18Markus1984/ESP_Logger/docs/images/hero_A.png

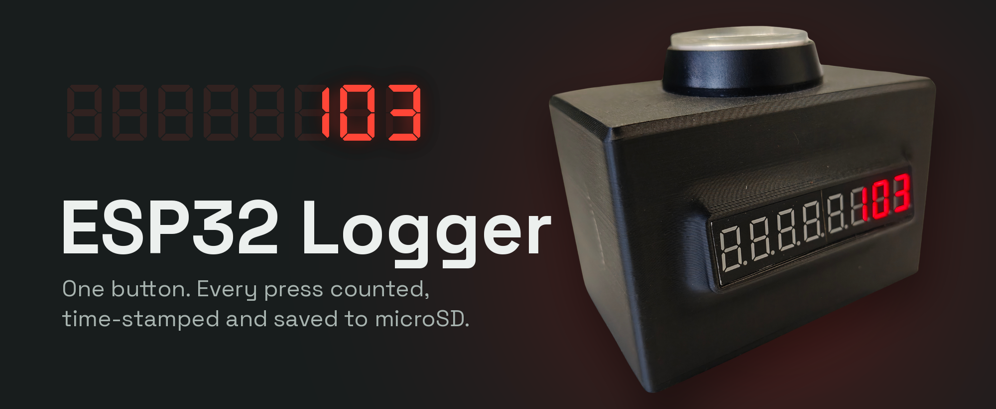
docs/images/hero_A.png
