18Markus1984/ESP_Logger/PCB/BesucherTasterPlatine/V1.3OhneCopperFill/BesucherZähler_etch_copper_top.pdf

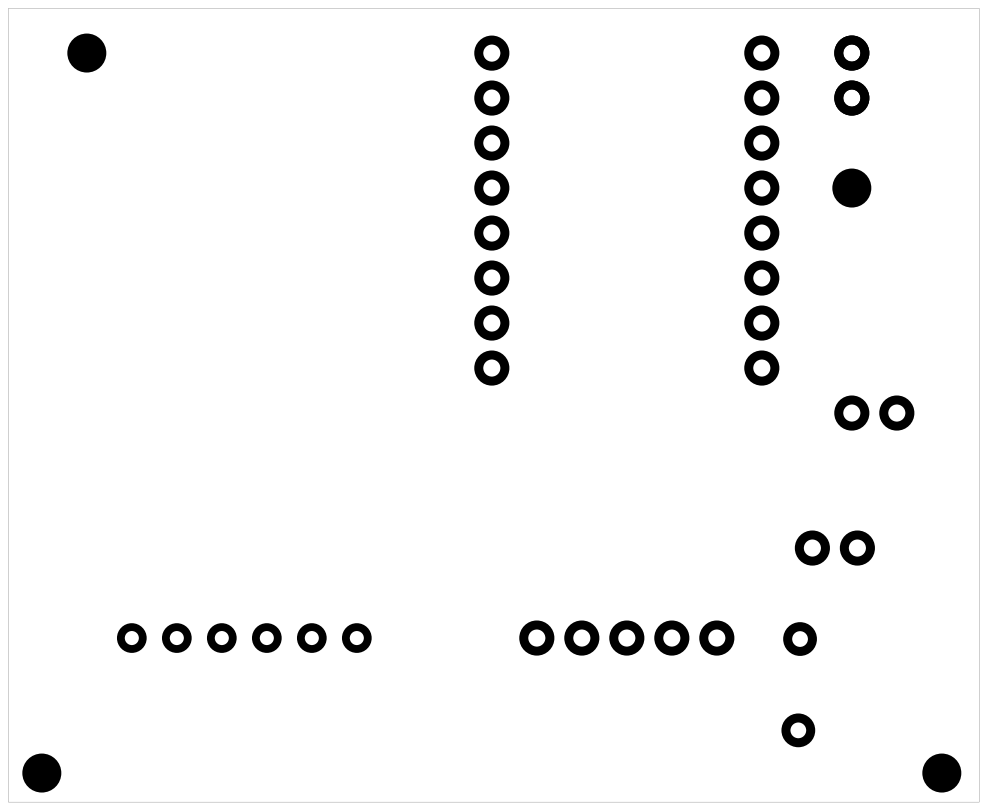
[picture p43: page 1]
