18Markus1984/ESP_Logger/PCB/BesucherTasterPlatine/V1.3OhneCopperFill/BesucherZähler_etch_copper_top_mirror.pdf

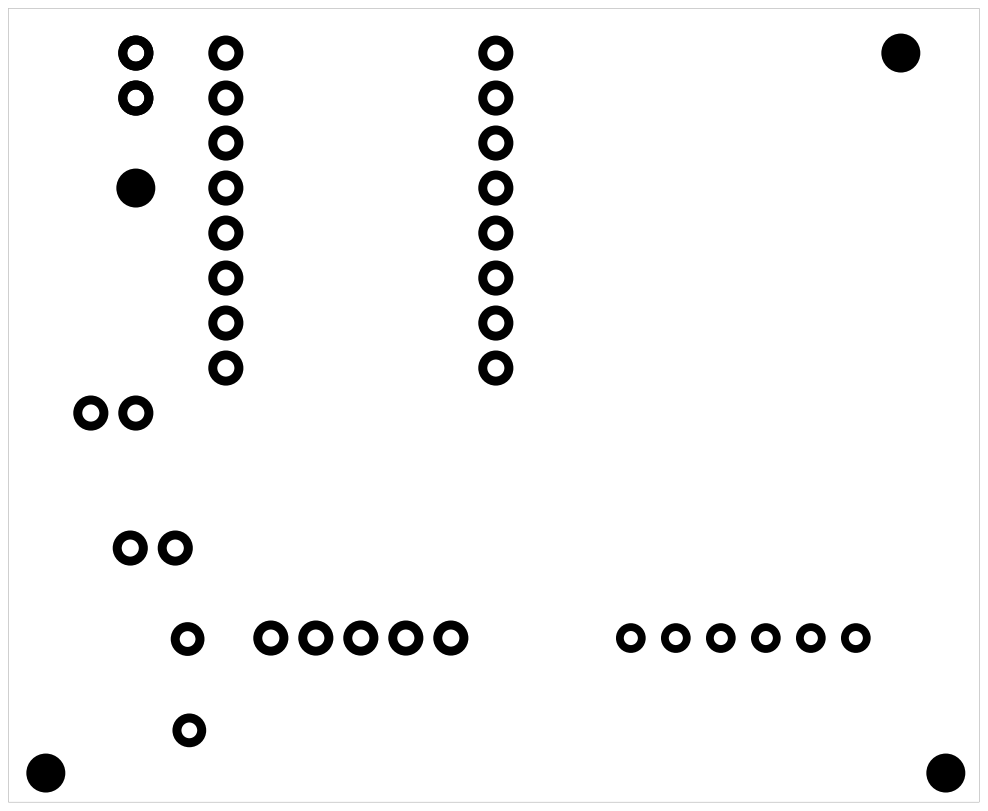
[picture p44: page 1]
