18Markus1984/ESP_Logger/PCB/BesucherTasterPlatine/V1.3OhneCopperFill/BesucherZähler_etch_mask_bottom.pdf

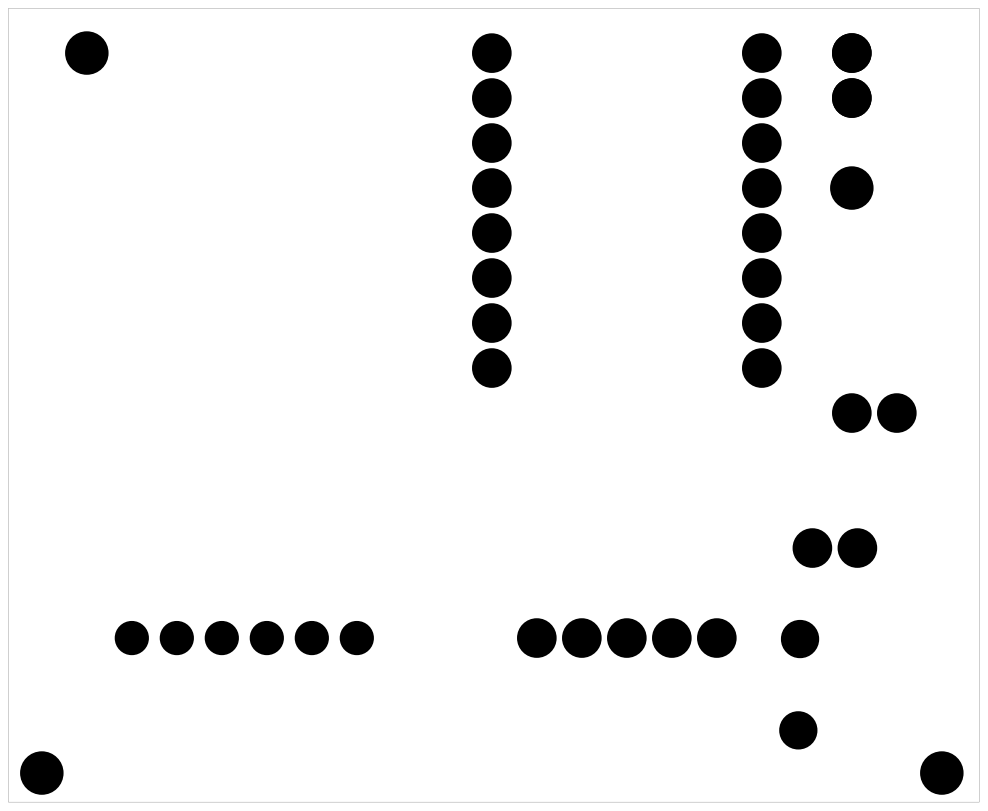
[picture p45: page 1]
