18Markus1984/ESP_Logger/PCB/BesucherTasterPlatine/V1.3OhneCopperFill/BesucherZähler_etch_mask_bottom_mirror.pdf

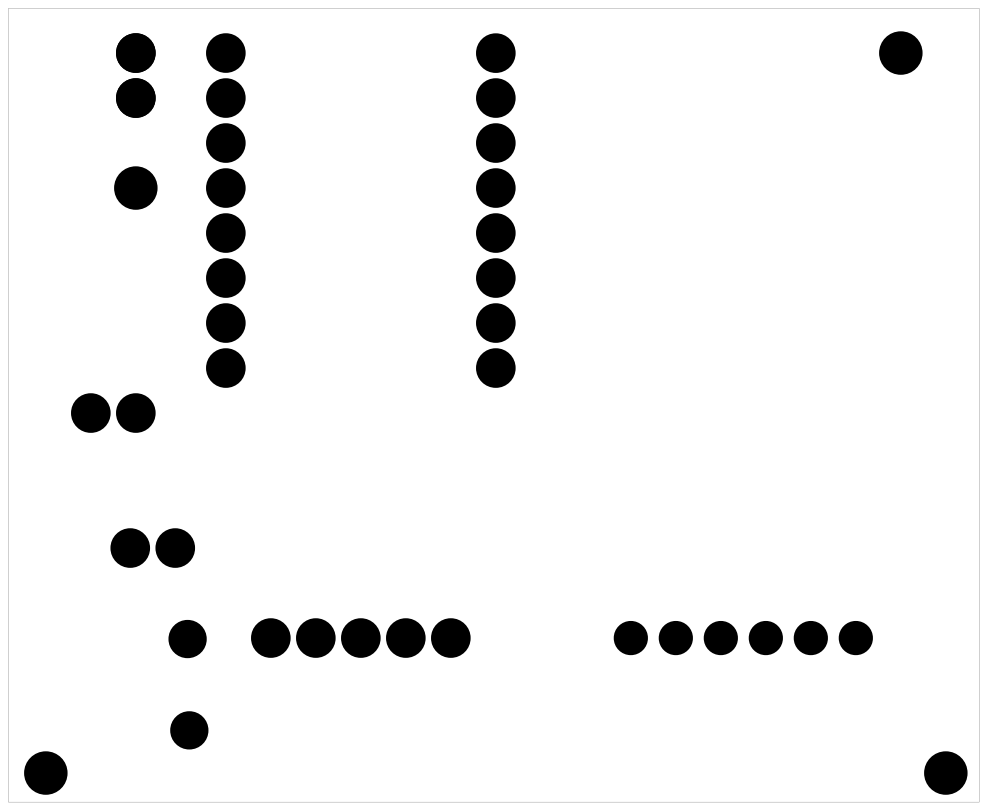
[picture p46: page 1]
