18Markus1984/ESP_Logger/PCB/BesucherTasterPlatine/V1.3OhneCopperFill/BesucherZähler_etch_silk_bottom.pdf

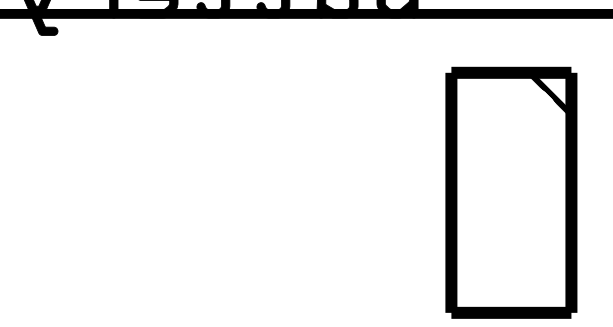
[picture p47: page 1]
