18Markus1984/ESP_Logger/PCB/BesucherTasterPlatine/V1.3OhneCopperFill/BesucherZähler_etch_silk_bottom_mirror.pdf

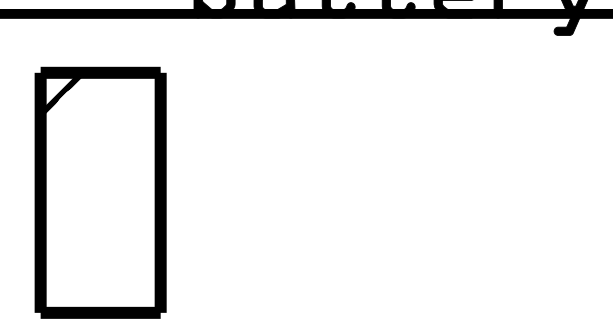
[picture p48: page 1]
