18Markus1984/ESP_Logger/PCB/BesucherTasterPlatine/V1.3OhneCopperFill/BesucherZähler_etch_silk_top_mirror.pdf

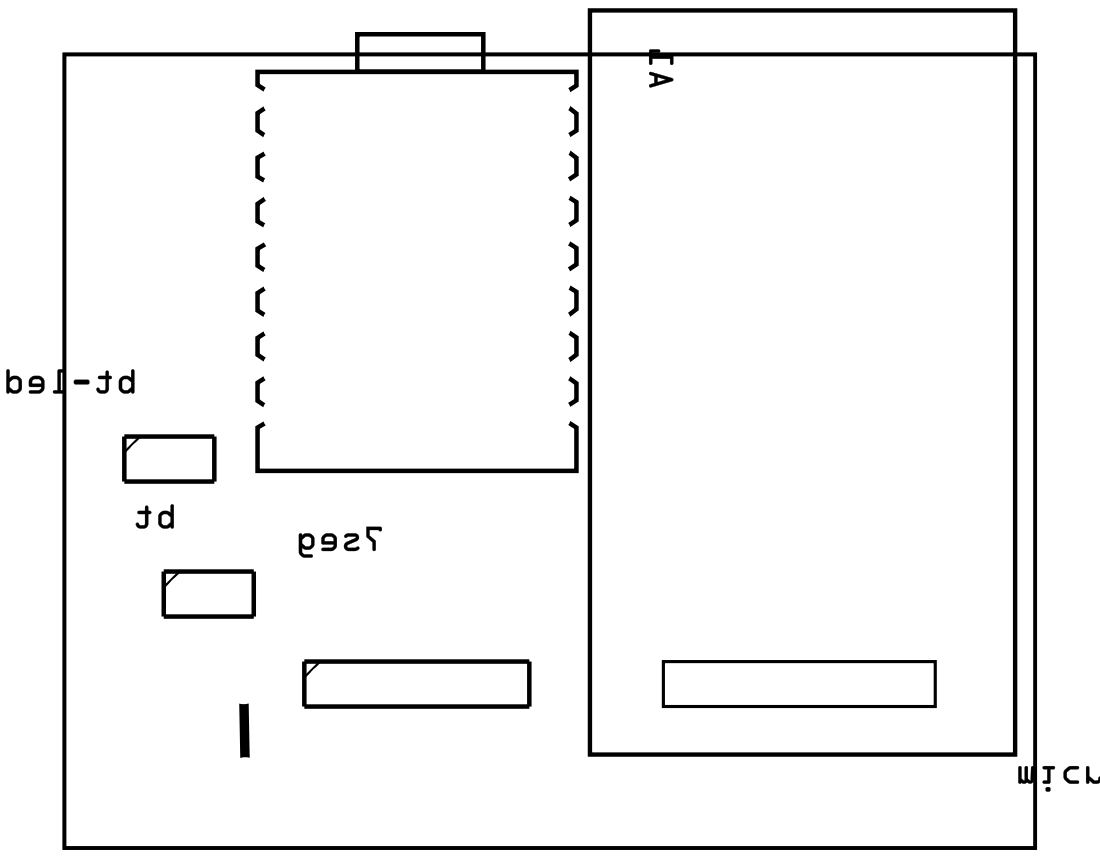
[picture p50: page 1]
