18Markus1984/ESP_Logger/PCB/BesucherTasterPlatine/V2.2_S2Mini/BesucherZählerS2Mini_etch_copper_bottom.pdf

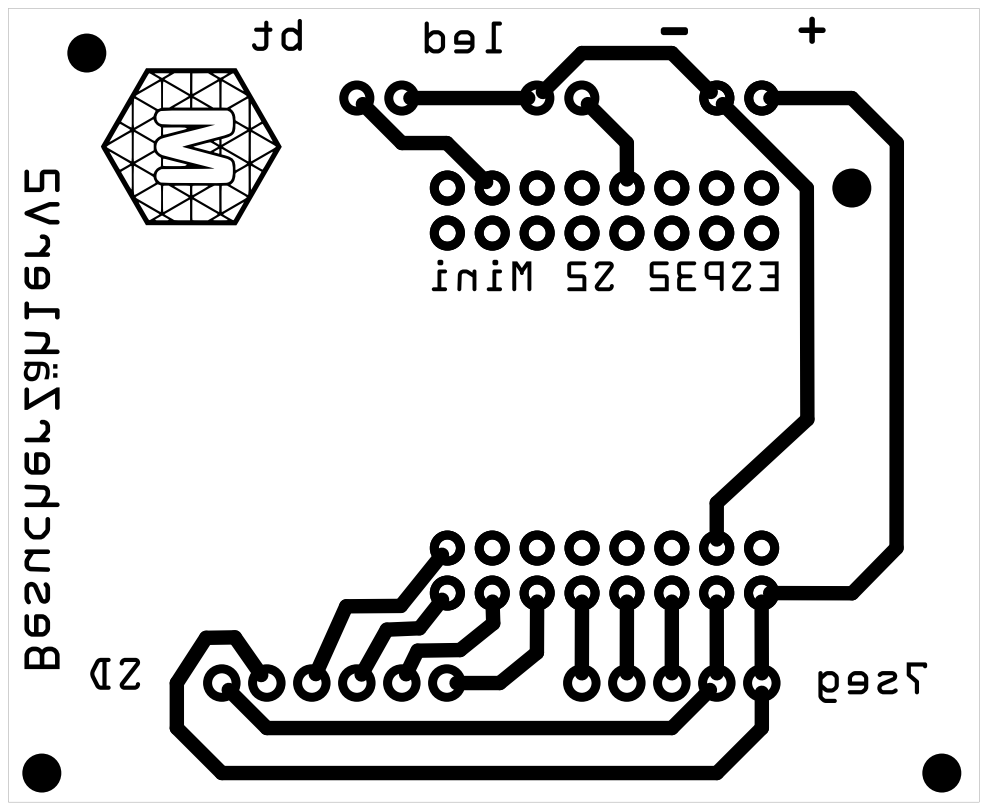
[picture p51: page 1]
