18Markus1984/ESP_Logger/PCB/BesucherTasterPlatine/V2.2_S2Mini/BesucherZählerS2Mini_etch_copper_top_mirror.pdf

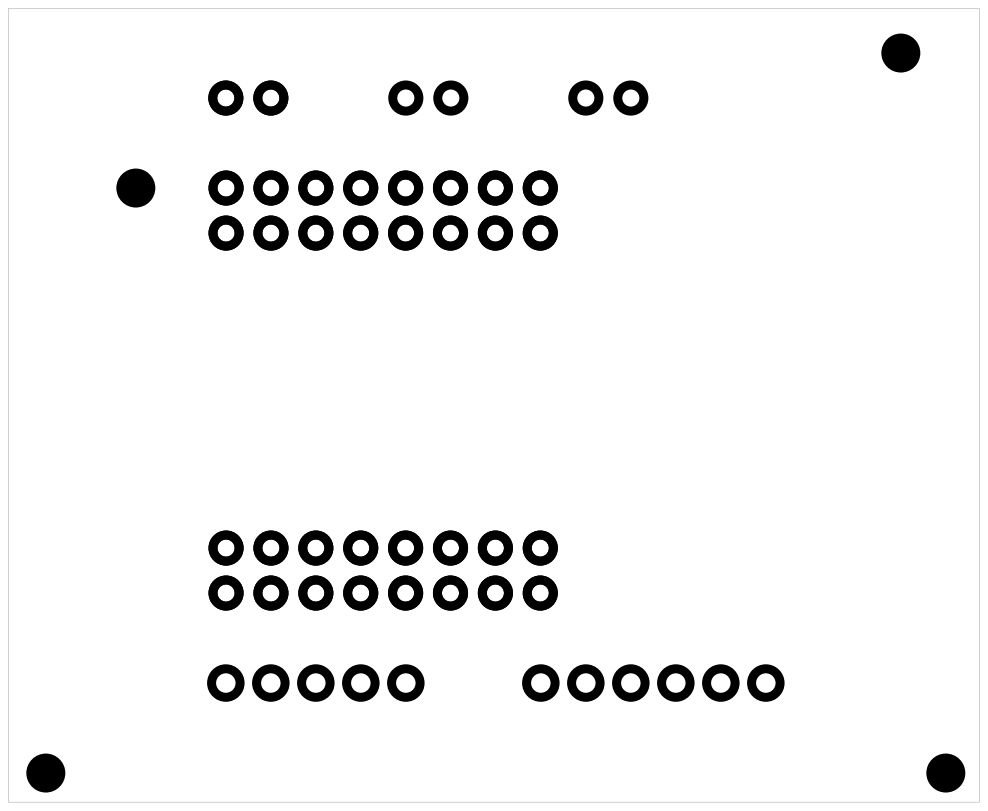
[picture p54: page 1]
