18Markus1984/ESP_Logger/PCB/BesucherTasterPlatine/V2.2_S2Mini/BesucherZählerS2Mini_etch_mask_bottom.pdf

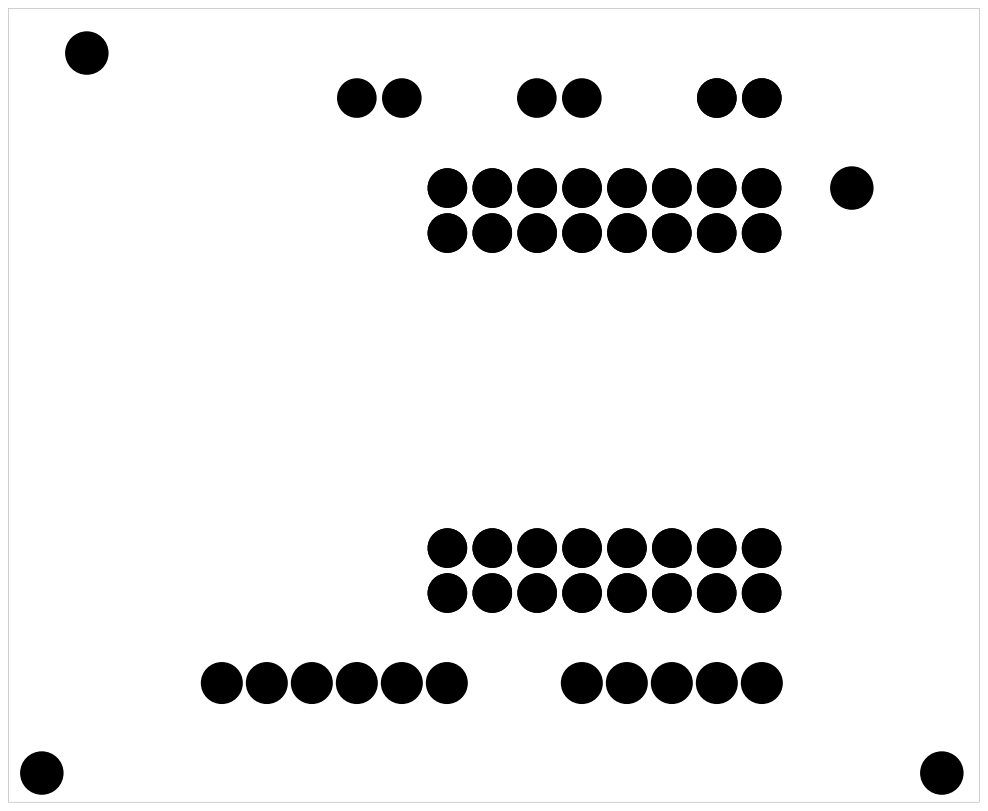
[picture p55: page 1]
