18Markus1984/ESP_Logger/PCB/BesucherTasterPlatine/V2.2_S2Mini/BesucherZählerS2Mini_etch_mask_bottom_mirror.pdf

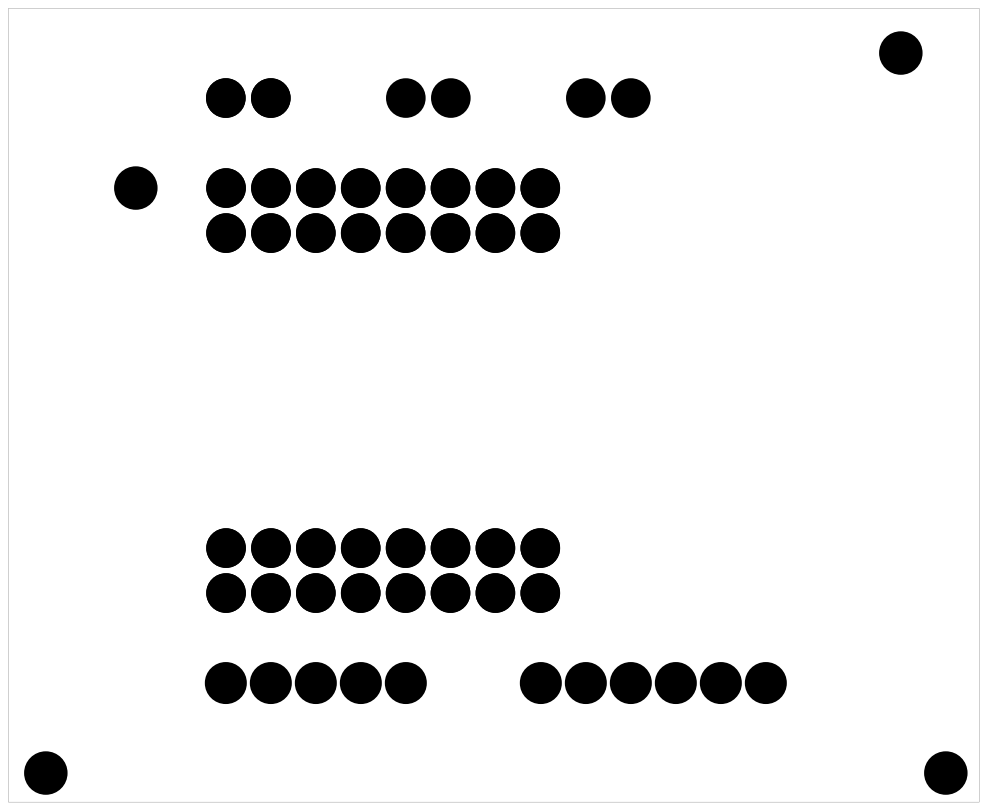
[picture p56: page 1]
