18Markus1984/ESP_Logger/PCB/BesucherTasterPlatine/V2.2_S2Mini/BesucherZählerS2Mini_etch_silk_bottom_mirror.pdf

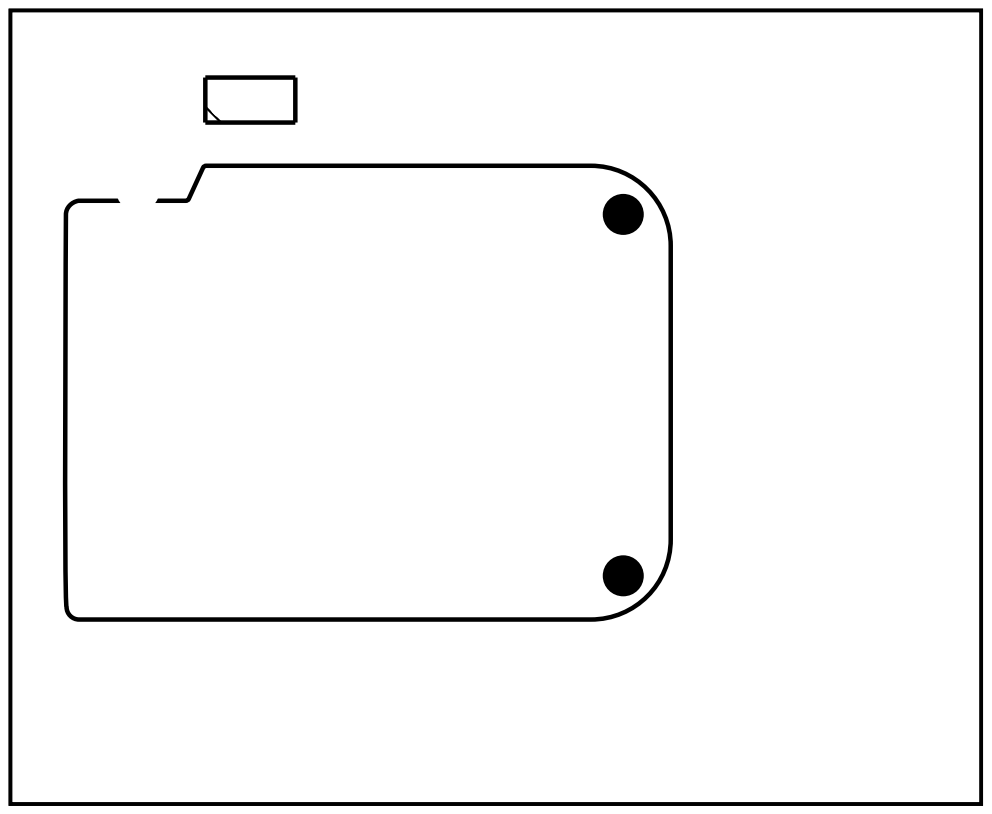
[picture p58: page 1]
