18Markus1984/ESP_Logger/PCB/BesucherTasterPlatine/V2.2_S2MiniGroundFill/BesucherZählerS2Mini_etch_copper_top.pdf

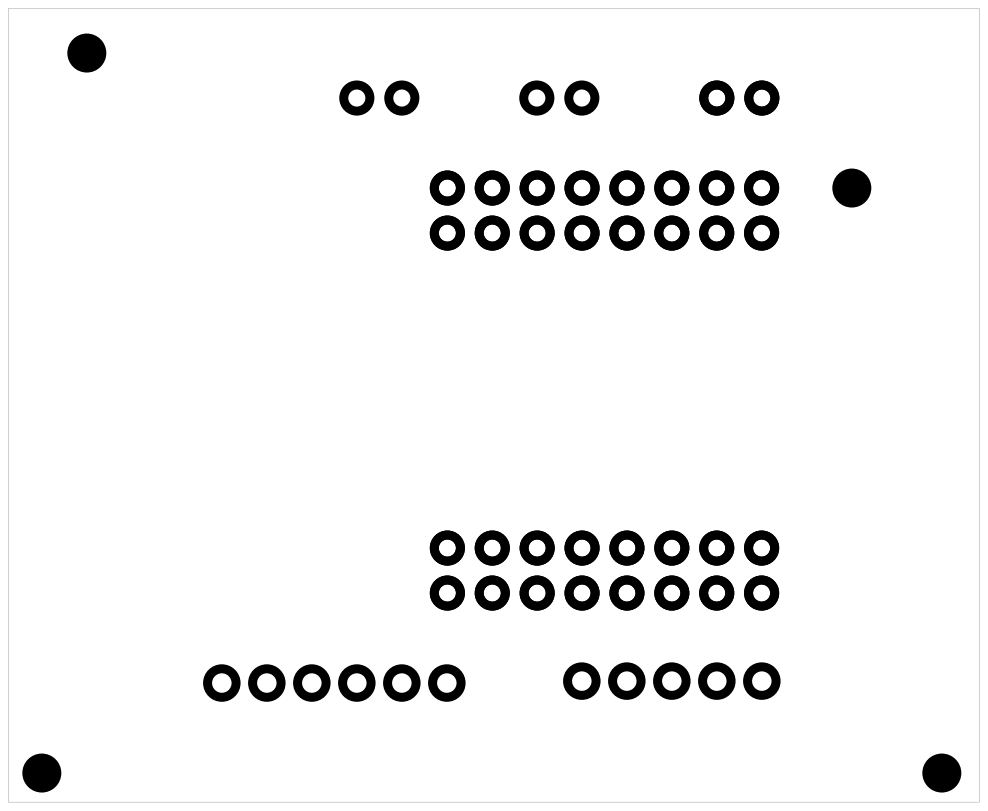
[picture p63: page 1]
