18Markus1984/ESP_Logger/PCB/BesucherTasterPlatine/V2.2_S2MiniGroundFill/BesucherZählerS2Mini_etch_mask_bottom.pdf

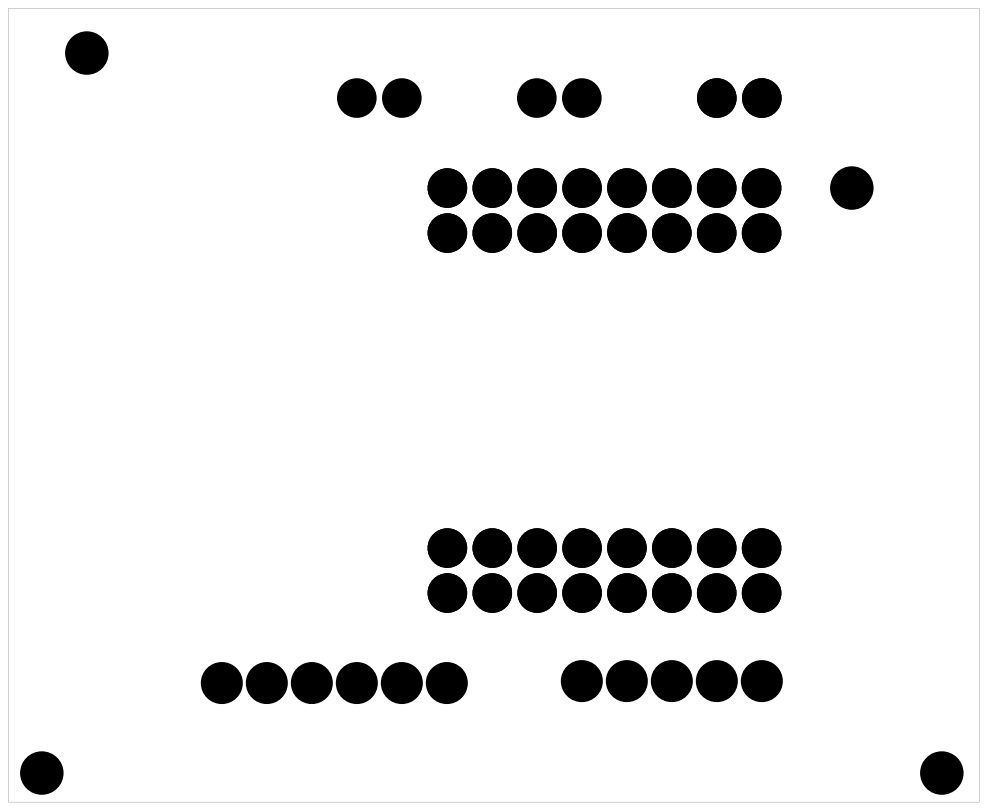
[picture p65: page 1]
