18Markus1984/ESP_Logger/PCB/BesucherTasterPlatine/V1.2/BesucherZähler_etch_copper_bottom.pdf

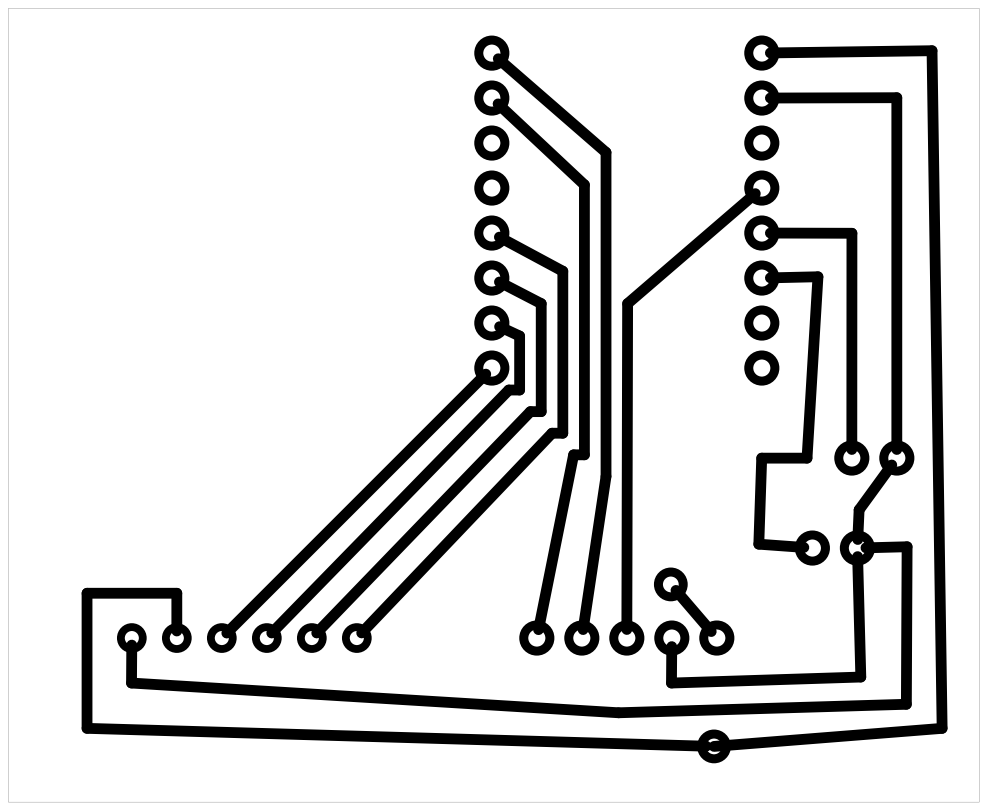
[picture p69: page 1]
