18Markus1984/ESP_Logger/PCB/BesucherTasterPlatine/V1.2/BesucherZähler_etch_copper_bottom_mirror.pdf

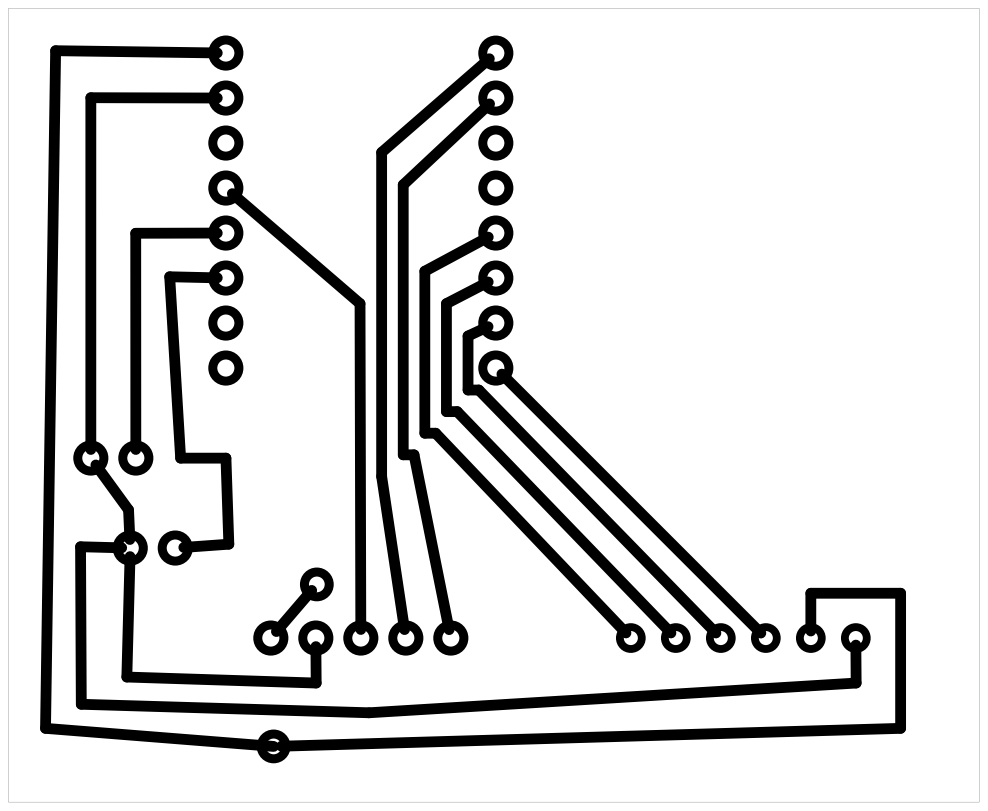
[picture p70: page 1]
