18Markus1984/ESP_Logger/PCB/BesucherTasterPlatine/V1.2/BesucherZähler_etch_mask_bottom.pdf

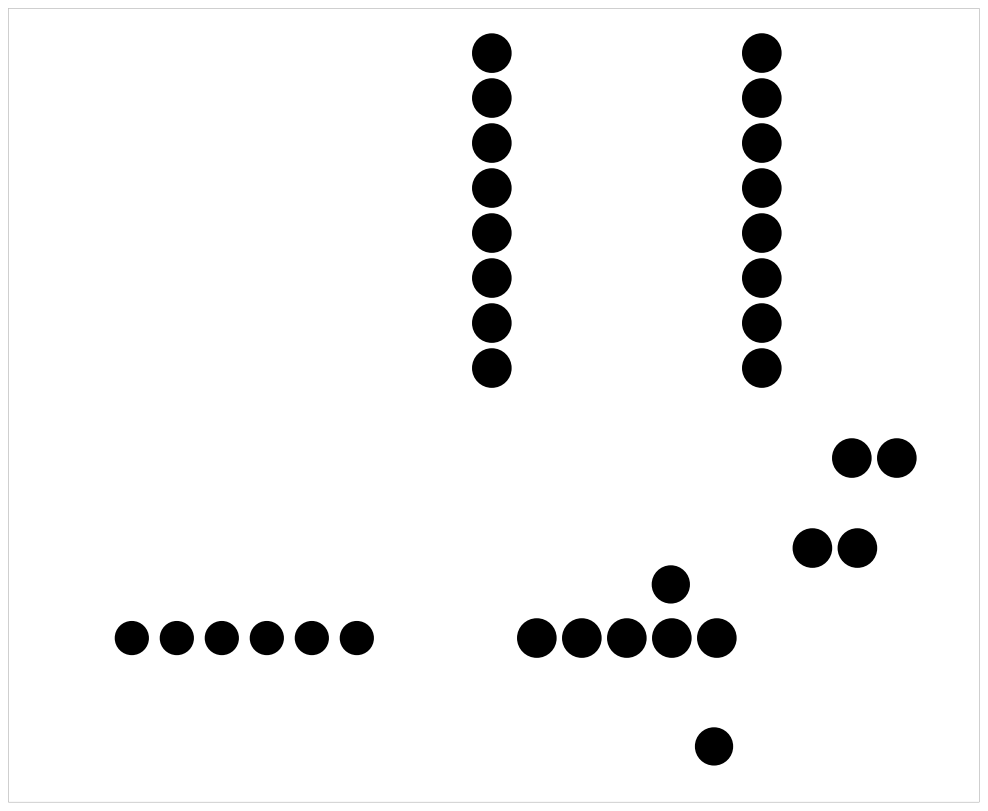
[picture p71: page 1]
