18Markus1984/ESP_Logger/PCB/BesucherTasterPlatine/V1.2/BesucherZähler_etch_mask_bottom_mirror.pdf

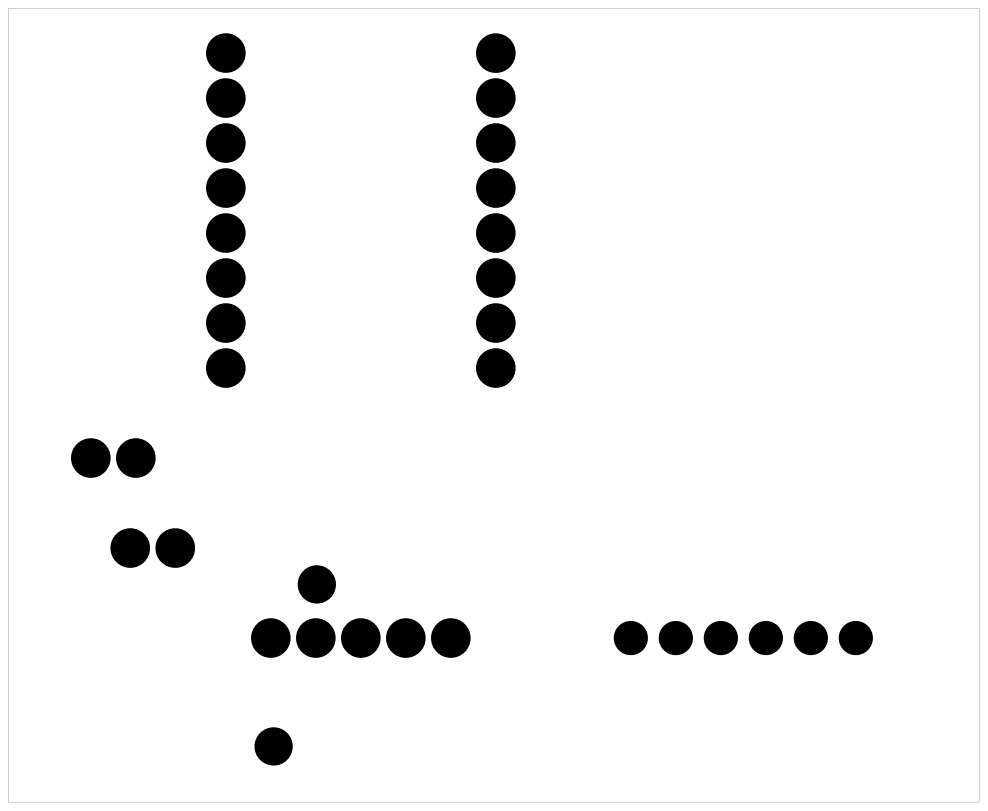
[picture p72: page 1]
