18Markus1984/ESP_Logger/PCB/BesucherTasterPlatine/V1.2/BesucherZähler_etch_silk_bottom.pdf

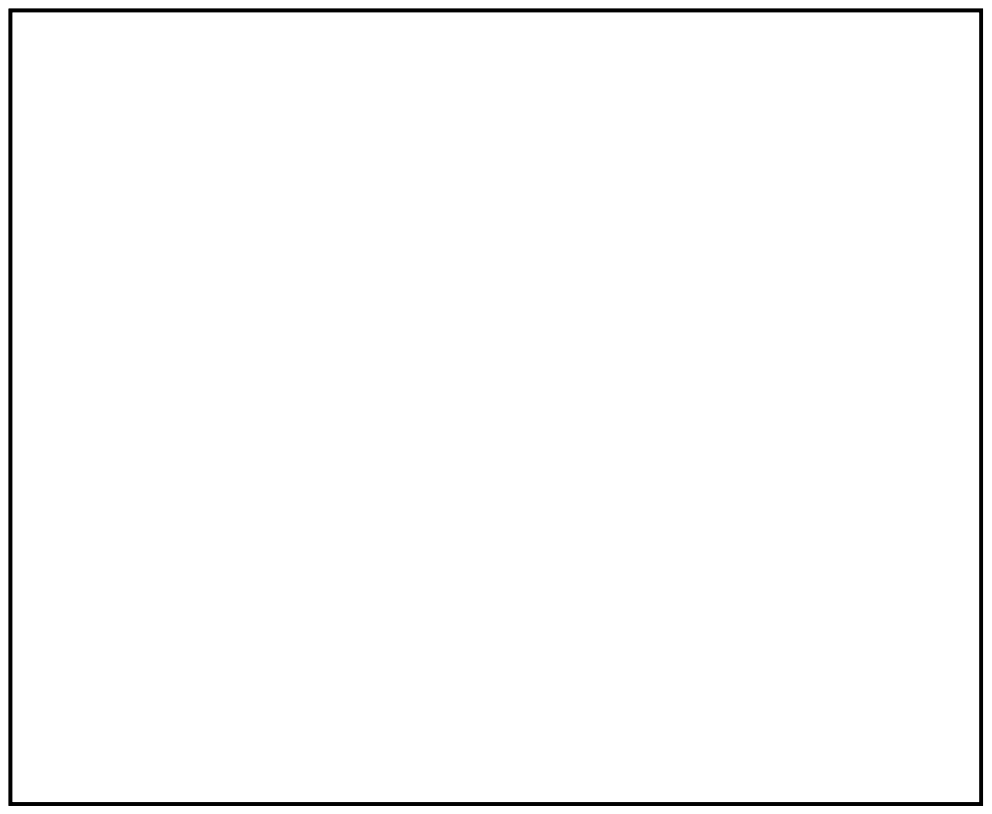
[picture p73: page 1]
