18Markus1984/ESP_Logger/PCB/BesucherTasterPlatine/V1/BesucherZähler_etch_copper_bottom.pdf

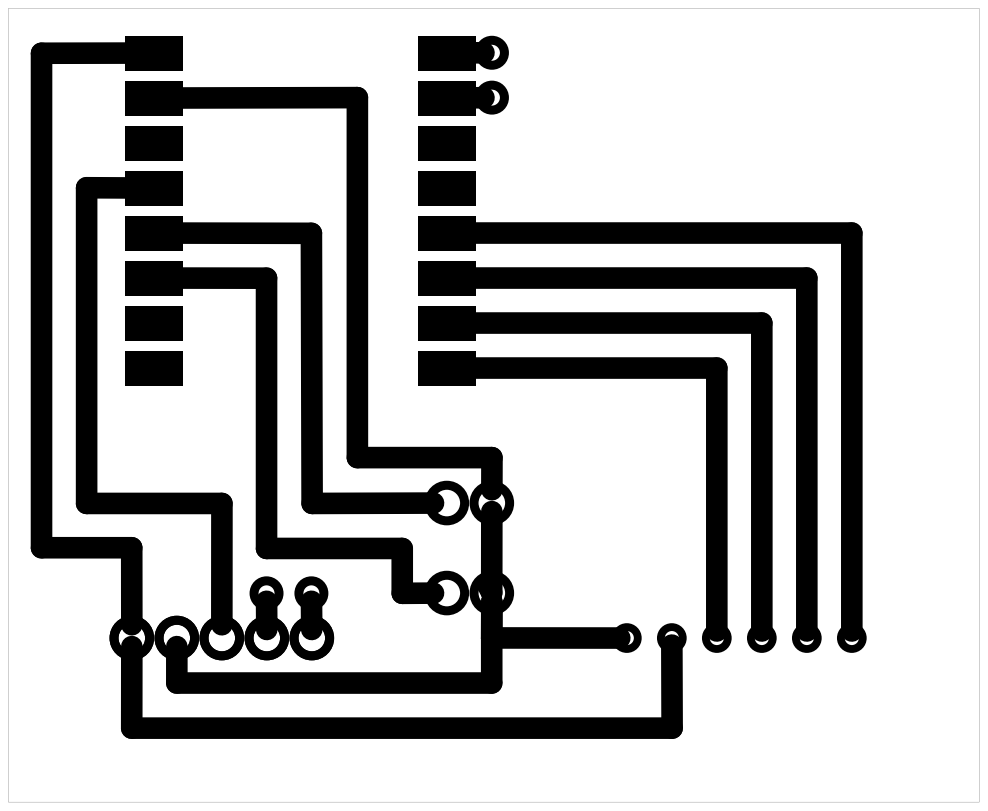
[picture p74: page 1]
