18Markus1984/ESP_Logger/PCB/BesucherTasterPlatine/V1/BesucherZähler_etch_copper_bottom_mirror.pdf

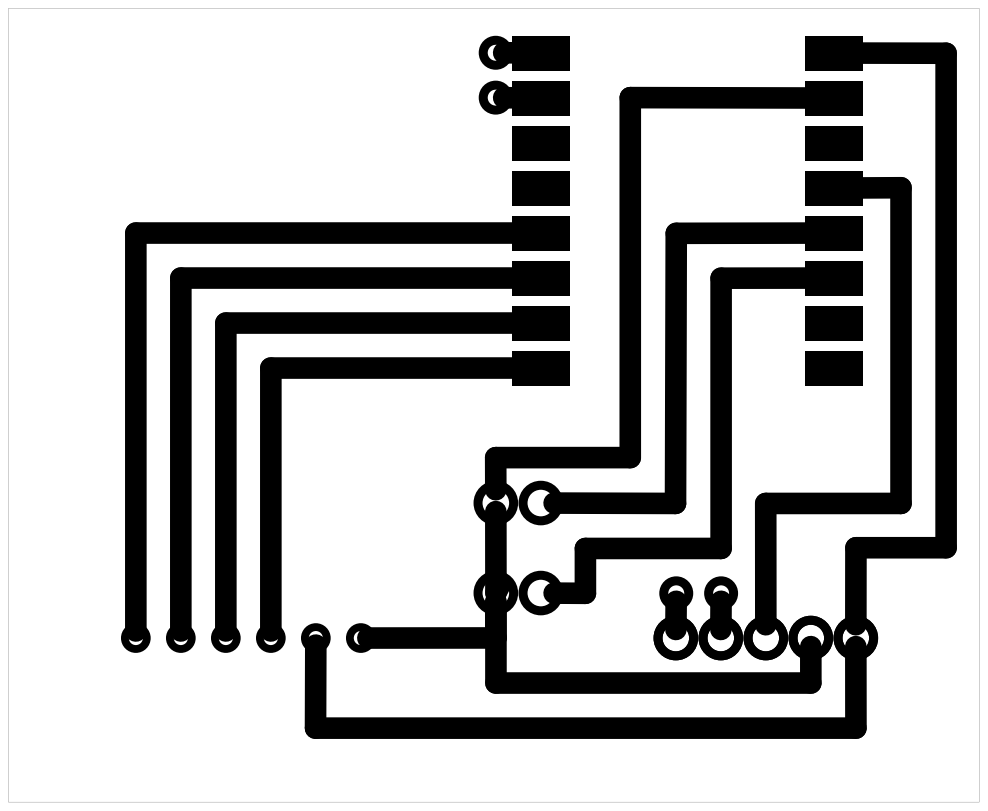
[picture p75: page 1]
