18Markus1984/ESP_Logger/PCB/BesucherTasterPlatine/V1/BesucherZähler_etch_mask_bottom.pdf

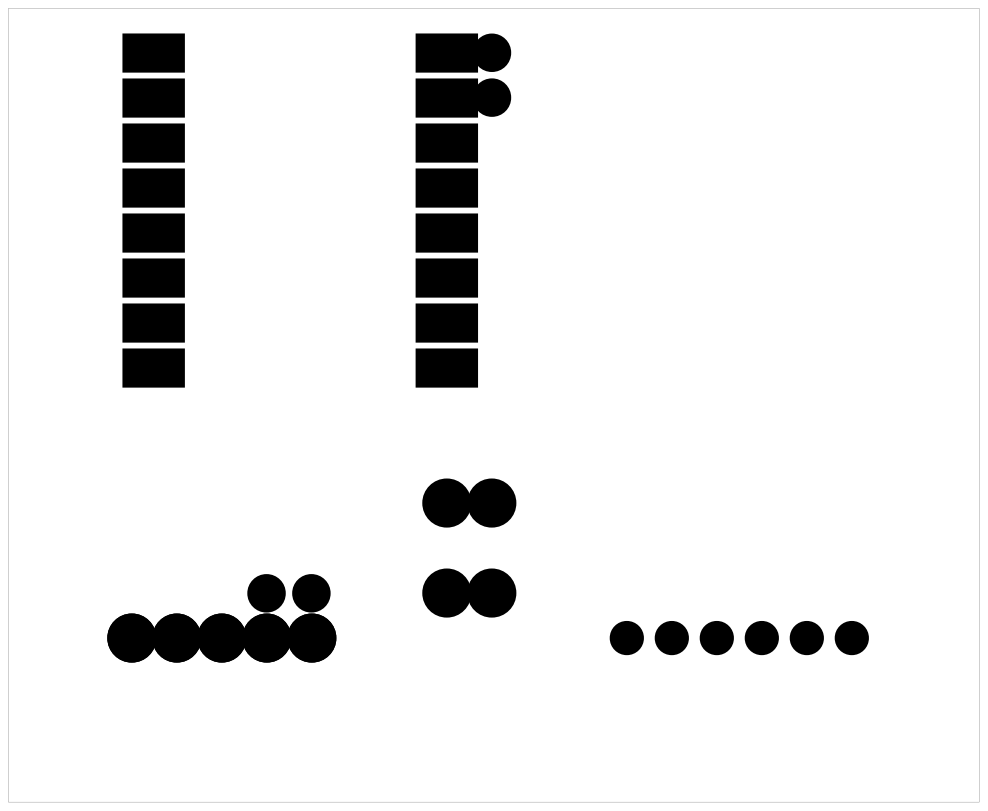
[picture p76: page 1]
