18Markus1984/ESP_Logger/PCB/BesucherTasterPlatine/V1/BesucherZähler_etch_mask_bottom_mirror.pdf

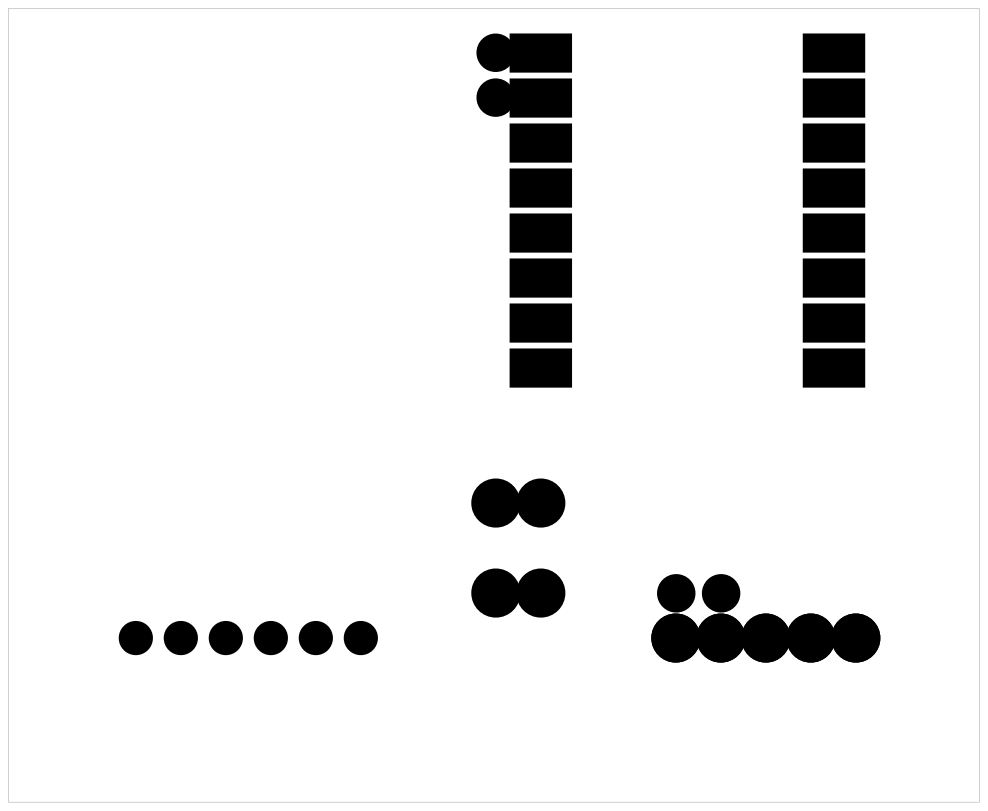
[picture p77: page 1]
