18Markus1984/ESP_Logger/PCB/BesucherTasterPlatine/V1/BesucherZähler_etch_silk_bottom.pdf

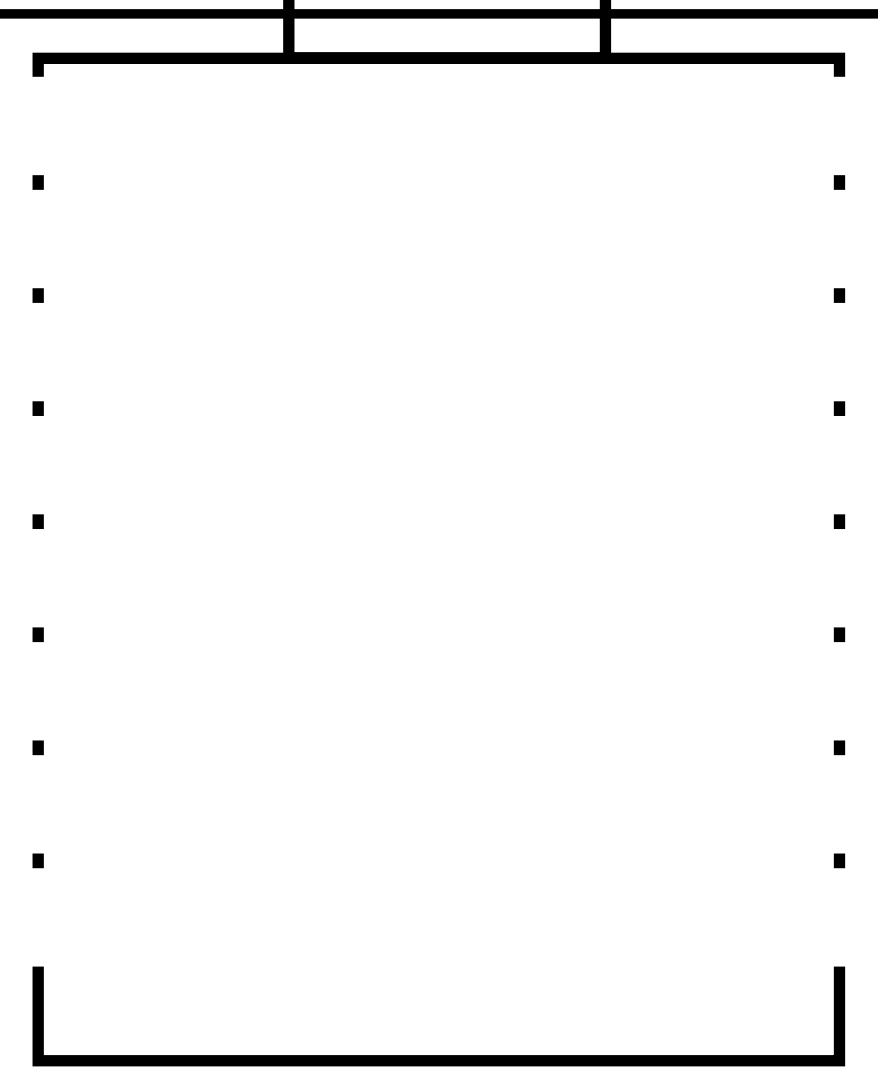
[picture p78: page 1]
