18Markus1984/ESP_Logger/PCB/BesucherTasterPlatine/V1/BesucherZähler_etch_silk_bottom_mirror.pdf

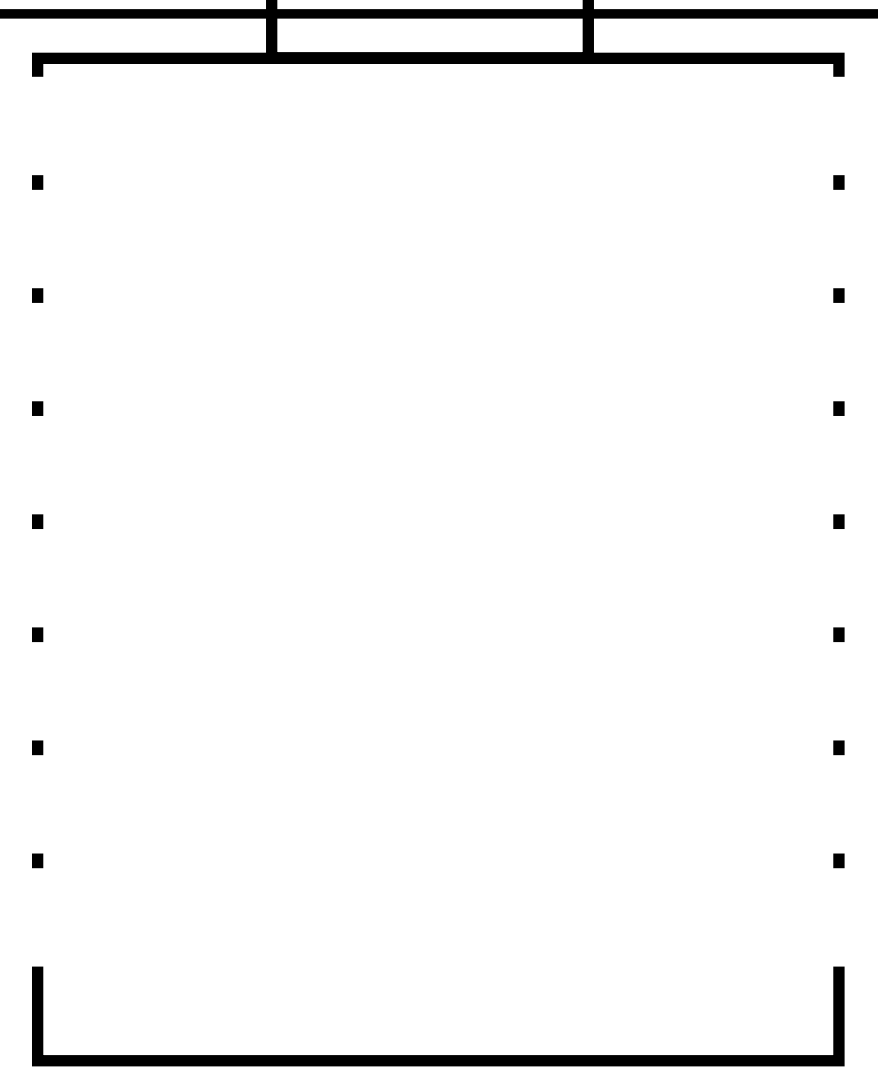
[picture p79: page 1]
