18Markus1984/ESP_Logger/PCB/BesucherTasterPlatine/V2.1_S2Mini/BesucherZählerS2Mini_etch_copper_bottom_mirror.pdf

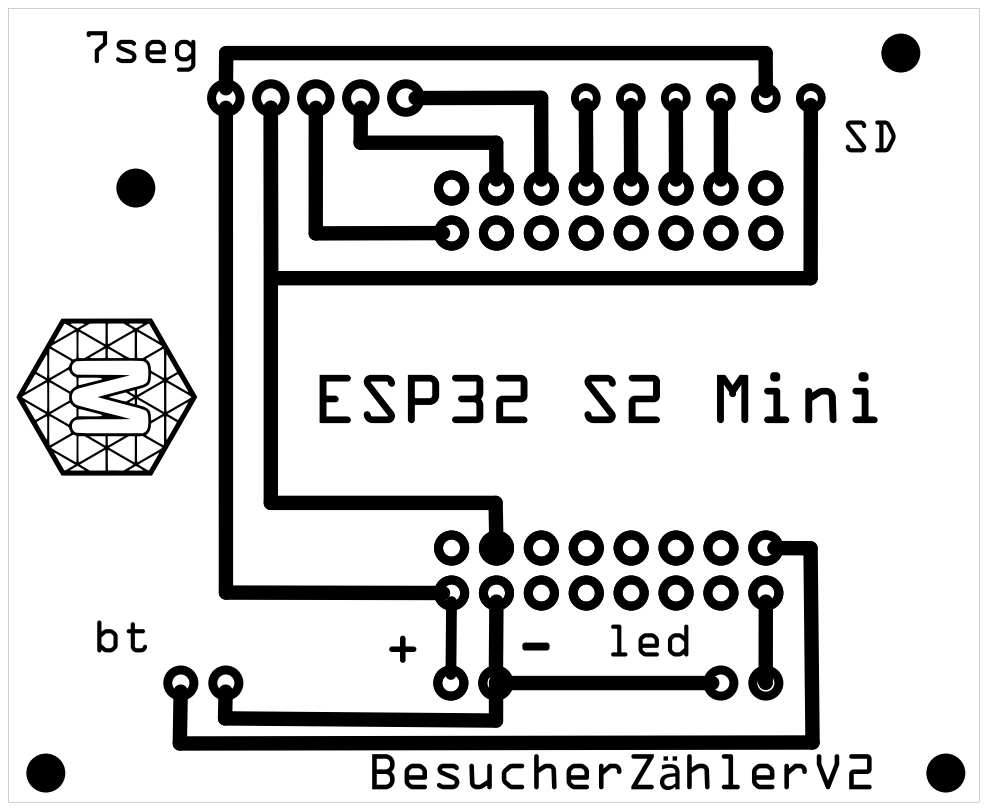
[picture p81: page 1]
